sjgray/C1581/Enhanced/PROTO1/_Pics/2024-02-05-pcb-render.png

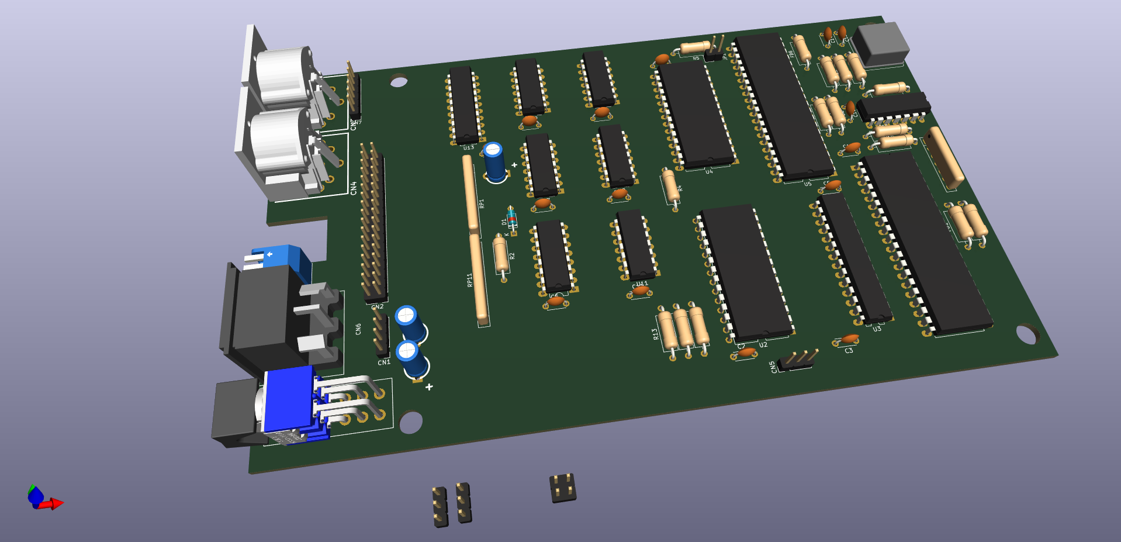
Enhanced/PROTO1/_Pics/2024-02-05-pcb-render.png
