sjgray/C1581/Enhanced/PROTO3/_Pics/render-top.jpg

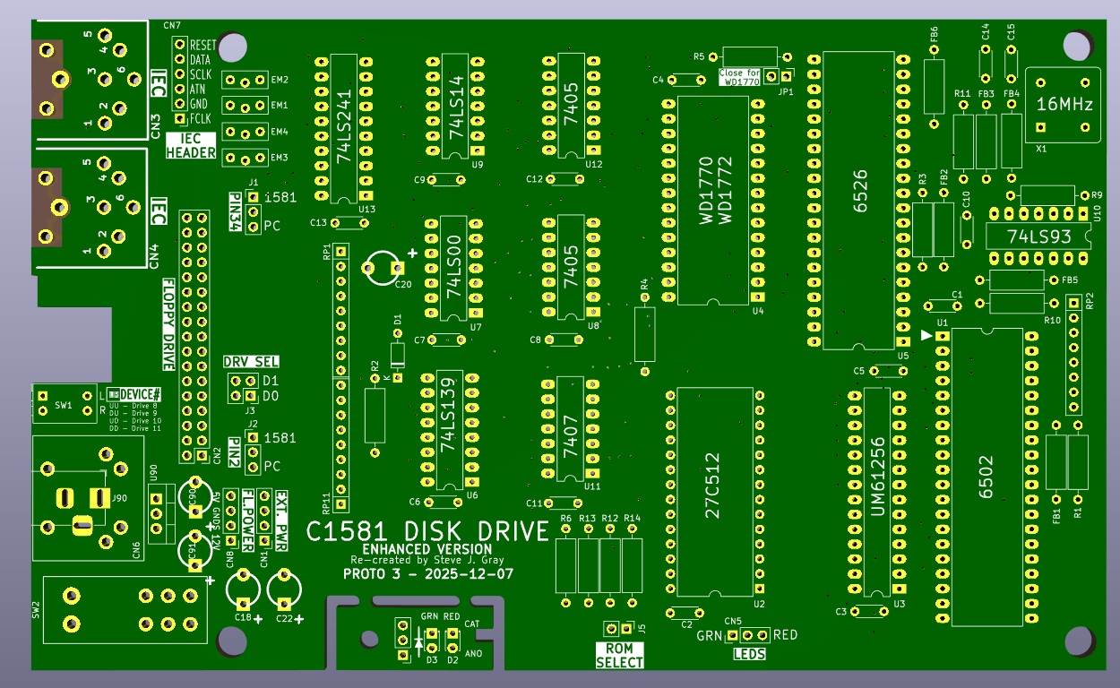
Enhanced/PROTO3/_Pics/render-top.jpg
