sjgray/C1581/Enhanced/PROTO3/C1581.jpg

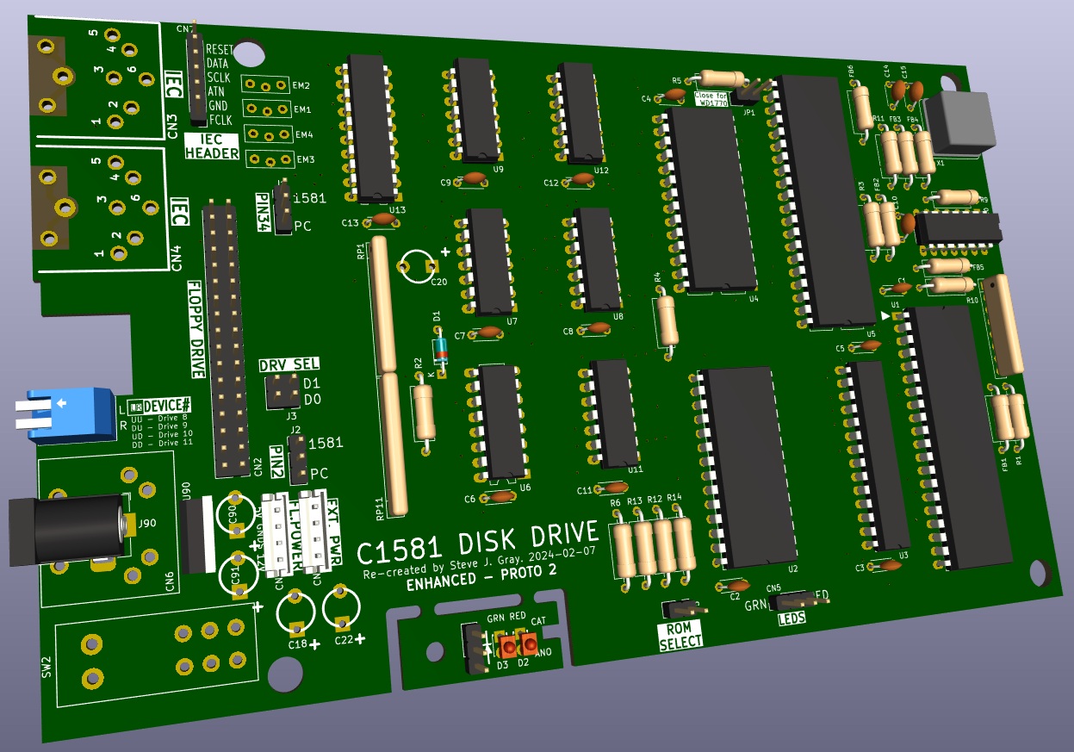
Enhanced/PROTO3/C1581.jpg
