sjgray/C1581/Internal/Proto3/_Pics/2025-12-02-Render-bot.jpg

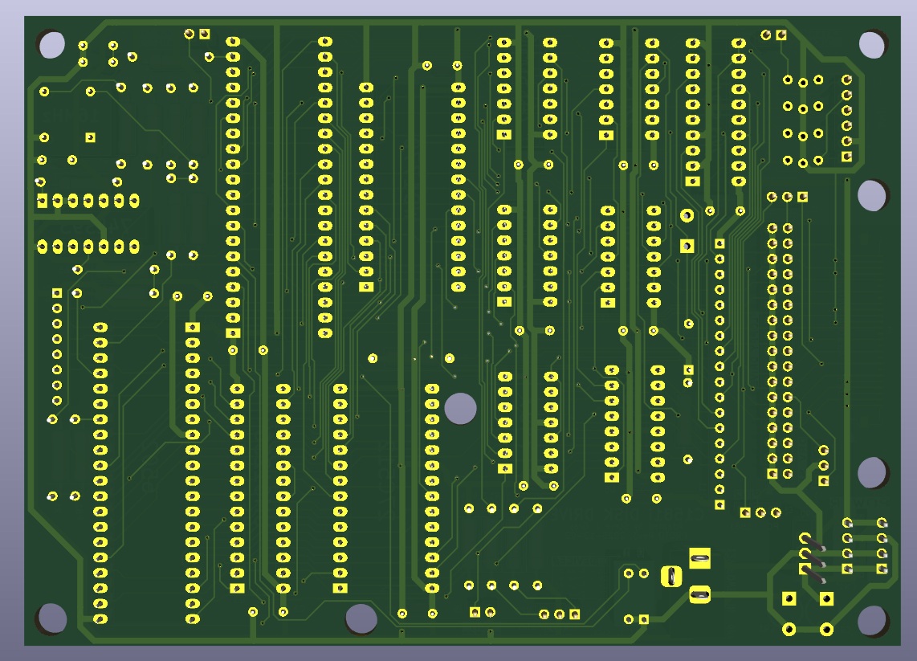
Internal/Proto3/_Pics/2025-12-02-Render-bot.jpg
