sjgray/C1581/Internal/Proto3/C1581i.jpg

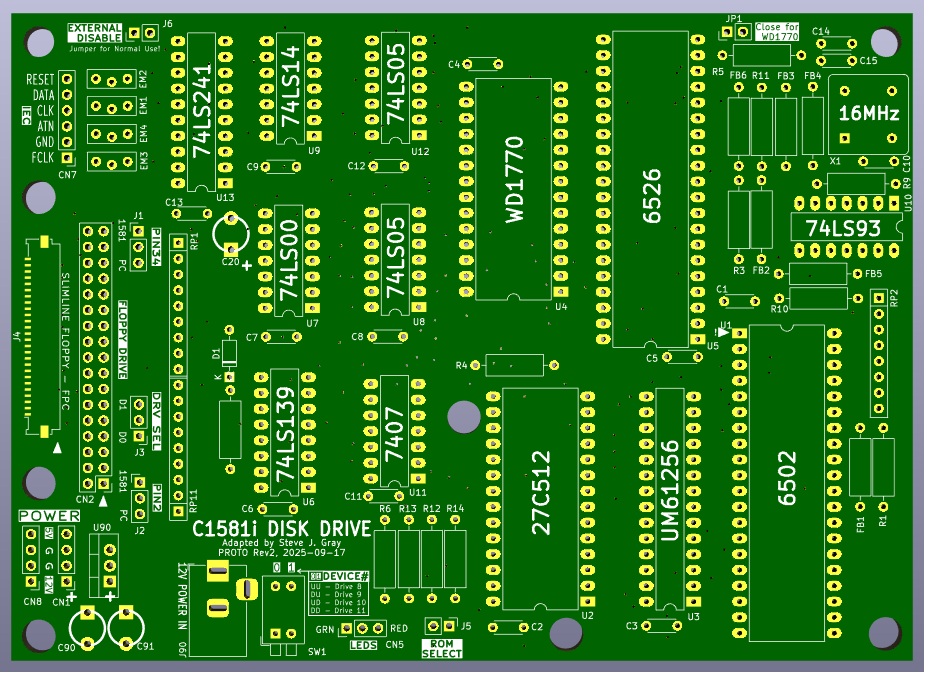
Internal/Proto3/C1581i.jpg
